johngarchie/xmas-icetube/firmware/config.h

#ifndef CONFIG_H
#define CONFIG_H

// XMAS-ICETUBE CLOCK DESIGN
//
// The xmas-icetube revision of the Ice Tube Clock requires a few
// firmware modifications.  The XMAS_DESIGN macro below enables these
// modifications, but breaks compatibility with the Adafruit Ice Tube
// Clock v1.1.
//
// When configuring this firmware for use with the xmas-icetube
// revision, the configuration macros for the following features
// should also be enabled:  the automatic dimmer hack, the software
// temperature compensated timekeeping, and the IV-18 to-spec hack.
//
//
// #define XMAS_DESIGN


// ADAFRUIT-STYLE BUTTONS
//
// By default, the xmas-icetube firmware uses a unique button scheme
// where there is one button mapped to each basic function:
//
//   enter/exit menu:  menu button
//   next:             plus button
//   select/set:       set button
//
// With the Adafruit button scheme, the buttons used for the first two
// functions depend on context:
//
//   enter/exit menu:  menu button when time is displayed,
//                     plus button when a menu label is displayed,
//                     menu button when a setting value is displayed
//   next:             menu button when a menu label is displayed,
//                     plus button when a setting value is displayed
//   select/set:       set button
//
// In addition to being simpler, the xmas button scheme works more
// intuitively with the xmas nested configuration menus.  Even so, some
// users still prefer the Adafruit scheme, typically for reasons of
// familiarity.  The following macro enables the Adafruit button scheme.
//
//
// #define ADAFRUIT_BUTTONS


// LOW BATTERY THRESHOLD
//
// After sleeping for ten minutes, system voltage should fall to whatever
// the battery is providing.  After that time, the microcontroller will
// check the system voltage.  If system voltage is below the following
// threshold, the clock will display a low battery warning ("bad batt")
// upon waking.
//
//
#define LOW_BATTERY_VOLTAGE 2600  // millivolts


// AUTOMATIC DIMMER HACK
//
// Defining the following macro enables support for Automatic dimming.
// This hack also allows for the clock display to be disabled at night
// (when dark).
//
// In the Adafruit Ice Tube Clock v1.1, this feature requires a
// pull-up resister to be installed in R4 and a CdS photoresistor to
// be installed in CT1.  CT1 is the two expansion pins nestled among
// L1, R4, and SPK.  I suggest using a 5.6k pull-up resistor with an
// Advanced Photonix Inc PDV-P8001 photoresistor.  Note that
// photoresistors purchased from Adafruit should behave like the
// PDV-P8001 and are acceptable substitutes.
//
// The automatic dimmer hack is discussed extensively on the
// Adafruit Clocks forum:
//
//   http://forums.adafruit.com/viewtopic.php?f=41&t=12932
//   http://forums.adafruit.com/viewtopic.php?p=219736#p219736
//
#define AUTOMATIC_DIMMER


// GPS TIMEKEEPING
//
// Defining the GPS_TIMEKEEPING macro below enables GPS detection on
// the ATmega's RX pin.  The connection speed is 9600 baud by default
// for compatibility with the Adafruit Ultimate GPS Module.  For more
// information, visit the following pages:
//
//   http://forums.adafruit.com/viewtopic.php?f=41&t=36873
//   http://www.ladyada.net/make/icetube/mods.html
//   http://forums.adafruit.com/viewtopic.php?f=41&t=32660
//
// In most cases, the clock should report an error if the GPS loses
// its fix.  But users with no GPS reception might want to disable the
// "gps lost" error message.  Those users will instead move their
// clocks to an area of good reception whenever they wish to
// syncronize the clock time with the GPS time.  To disable the GPS
// lost error message, comment out the GPS_LOST_ERROR_MSG macro below.
//
//
#define GPS_TIMEKEEPING
#define GPS_LOST_ERROR_MSG


// USART BAUD RATE
//
// The USART baud rate defined below is used for both the debugging
// output and GPS timekeeping.
//
//
#define USART_BAUDRATE 9600


// TEMPERATURE COMPENSATED CRYSTAL OSCILLATOR
//
// The following macro enables support for an external 32.768 kHz
// clock source such as a Maxim DS32kHz.  This hack is discussed in
// detail on the Adafruit Clocks forum:
//
//   http://forums.adafruit.com/viewtopic.php?f=41&t=14941
//
//
// #define EXTERNAL_CLOCK


// SOFTWARE TEMPERATURE COMPENSATED TIMEKEEPING
//
// This hack requires attaching a DS18B20 OneWire temperature sensor
// to ATmega328p PC1 pin, but unfortunately the internal temperature
// of the clock is above the ambient temperature.  As a result, this
// modification is not useful for displaying room temperature.
//
// This modification is, however, useful for temperature compensated
// timekeeping, and was primarily intended for the xmas-icetube
// hardware revision.  The DS32kHz, described in the previous section,
// is a simpler solution for the Adafruit Ice Tube Clock v1.1, but the
// DS18B20 will also work in the Adafruit design.   The DS18B20 should be
// installed in parasitic mode by grounding both the VDD and GND leads.
// The DQ lead should be connected to the PC1 pin on the ATmega328p and
// to PC5 via a 4.7k pull-up resistor.
//
// The XTAL_TURNOVER_TEMP macro specifies the temperature at which the
// crystal oscillates at maximum frequency in units of deg C / 16.
// The XTAL_FREQUENCY_COEF macro specifies the parabolic temperature
// dependence of the crystal in units -ppb / (deg C)^2.  For a
// turnover temperature of 25 deg C and a frequency coefficient of
// -0.034 ppm / (deg C)^2, XTAL_TURNOVER_TEMP should be defined as 400
// (25 * 16), and XTAL_FREQUENCY_COEF should be defined as 34
// (-0.034 * -1000).
//
// The technique for software temperature compensation is described in
// the following thread:
//
//   http://forums.adafruit.com/viewtopic.php?f=41&t=43998
//
// WARNING:  If your clock is modified for the original extended
// battery hack, which shorts the ATmega328P PC1 pin to ground,
// enabling the macros below might damage your clock!  The original
// extended battery hack is described in the following thread:
//
//   http://forums.adafruit.com/viewtopic.php?t=36697
// 
//
// #define TEMPERATURE_SENSOR
// #define XTAL_TURNOVER_TEMP  400  // deg C / 16
// #define XTAL_FREQUENCY_COEF 34   // -ppb / (deg C)^2


// BIRTHDAY ALARM
//
// If BDAY_ALARM_MONTH and BDAY_ALARM_DAY are defined, the alarm
// sound on that day will always be "For He's a Jolly Good Fellow,"
// regardless of the alarm sound set in the menus.
//
//
// #define BDAY_ALARM_MONTH 5
// #define BDAY_ALARM_DAY   1


// DISPLAY BRIGHTNESS / BOOST CONFIGURATION
//
// VFD displays lose brightness as they age, but increasing the
// grid/segment voltage can extend the useful life.  This voltage
// is controlled by the OCR0A register, and OCR0A is set by
//
//   OCR0A = OCR0A_MIN + OCR0A_SCALE * brightness
//
// where brightness is 0-10 as set through the configuration menu.
// The grid/segment voltage can be roughly estimated by
//
//   voltage = OCR0A / 4 + 6
//
// The IV-18 display has an absolute maximum grid/segment voltage of
// 70 volts, but on the Adafruit Ice Tube Clock, a Zener diode prevents
// this from exceeding 60 volts.  And the clock's fuse might blow before
// that point, so the hardware will ensure that the grid/segment voltage
// maximum is never exceeded.
//
// For a dim display, I suggest setting OCR0A_MIN to 30 and OCR0A_SCALE
// to 14.  If the fuse blows or becomes warm during operation, reduce
// OCR0A_SCALE or install a higher power fuse.
//
//
#define OCR0A_MIN   20
#define OCR0A_SCALE 11
#define OCR0A_MAX OCR0A_MIN + 10 * OCR0A_SCALE


// DISPLAY MULTIPLEXING ALGORITHM
//
// The following multiplexing options define how the display should be
// multiplexed.
//
// Digit multiplexing displays each digit in rapid succession.
// Although this is the standard way to do multiplexing, there might
// be slight ghosting, especially of decimals at higher boost voltage.
//
// I recommend digit multiplexing for use with the Adafruit Ice Tube
// Clock v1.1, without the to-spec hack.
//
// Subdigit multiplexing is similar to digit multiplexing, but
// displays each digit twice--once showing only segments B, C, and H
// (those lit when displaying "1.") and once showing only the other
// segments.  This method eliminates ghosting, but reduces overall
// brightness.
//
// I recommend subdigit multiplexing for use with the to-spec hack and
// the xmas-icetube hardware revision.  The reduction in overall
// brightness is a benefit here, as the minimum brightness attainable
// with PWM brightness control and digit multiplexing is a bit too
// bright.  And the maximum brightness with plain PWM and digit
// multiplexing is unnecessarally bright.
//
// Segment multiplexing displays each segment (on all digits where
// that segment is displayed) in rapid succession.  This method
// eliminates ghosting, and the maximum brightness is similar to that
// with digit multiplexing.  But the per-digit brightness adjustment
// is not available when using this method.
//
// I do not recommend segment multiplexing, but left the feature in
// the code in case anyone wants to play with it.  The problem with
// segment multiplexing is that resistance through the MAX6921
// limits current on each segment, so if one segment is displayed on
// many digits, that segment will be dimmer than if one segment is
// displayed on only a few digits.  Also, more current will flow
// through segments with the least resistance (at the right of the
// display), so those digits appear slightly brighter.
//
#define DIGIT_MULTIPLEXING
// #define SUBDIGIT_MULTIPLEXING
// #define SEGMENT_MULTIPLEXING


// IV-18 TO-SPEC HACK
//
// The Adafruit Ice Tube Clock v1.1 does not drive the IV-18 VFD tube
// to specifications, but with some rewiring and additional circuitry,
// enabling the following macros will drive the IV-18 tube as
// intended.  The following thread on the Adafruit Clocks forum
// describes the required hardware modifications for this hack:
//
//   http://forums.adafruit.com/viewtopic.php?f=41&t=41811
//
//
// #define VFD_TO_SPEC


// TO-SPEC BRIGHTNESS ADJUSTMENT METHOD
//
// These options should only be used with the to-spec hack above.
//
// With the to-spec hack, brightness may be controlled with boost
// voltage, pulse width modulation (PWM), or both.  I recommend
// controlling brightness with PWM only.
//
// If neither OCR0A_VALUE nor OCR0B_PWM_DISABLE is defined, brightness
// will be controlled by both boost voltage and PWM.
//
// If only OCR0A_VALUE is defined, the boost voltage will be fixed,
// and brightness will be controlled by PWM (recommended).
//
// If only OCR0B_PWM_DISABLE is defined, brightness will be controlled
// by the boost voltage.
//
// Defining OCR0A_VALUE and OCR0B_PWM_DISABLE is possible, but doing
// so will lock the display to a constant brightness and break the
// menu-configurable brightness adjustment.
//
// If D1 is a power blocking diode (as in the xmas-icetube hardware
// revision), I suggest an OCR0A_VALUE of 192.  If D1 is a Schottky
// diode (as in the original Adafruit design), I suggest an OCR0A_VALUE
// value of 128.  Ideally, the exact value should be tuned for your
// particular clock:  OCR0A_VALUE should be large enough such that the
// boost circuit generates just over 50v with the display installed
// and at maximum brightness, but OCR0A_VALUE should be no larger than
// necessary to prevent excessive voltage from being lost through the
// Zener diode.
//
//
// #define OCR0A_VALUE 128
// #define OCR0B_PWM_DISABLE


// TO-SPEC FILAMENT DRIVER METHOD
//
// The options below should only be used with the to-spec hack above.
// To drive the filament to specifications, do not define any of the
// filament current or voltage macros below.
//
// Some tubes may make a humming or whining sound when driven with AC.
// If the noise is unacceptable, the frequency can be divided with
// FILAMENT_FREQUENCY_DIV.  For example, if FILAMENT_FREQUENCY_DIV macro
// is defined as 3, the AC frequency will be 12/3 = 4 kHz.  The AC
// frequency may be divided by any value below 256.
//
// Although not to-spec, a sure-fire way to eliminate hum is to simply
// drive the filament with DC.  With a high boost voltage, there
// should not be a noticeable brightness gradient.
//
// Defining the FILAMENT_DRIVE_DC_FWD macro will drive the display
// with direct current instead of alternating current.  Current will
// flow from right to left across the display.  Defining the
// FILAMENT_DRIVE_DC_REV macro will use direct current flowing from
// left to right across the display.
//
// Defining either FILAMENT_VOLTAGE_3_3 or FILAMENT_VOLTAGE_2_5 will
// reduce the filament voltage to either 3.3 or 2.5 volts,
// respectively.  Voltage is reduced by changing the duty cycle from
// 100% to either 66% or 50%.  These macros also affect drive
// frequency; if the FILAMENT_FREQUENCY_DIV macro is undefined (or
// defined as 1), the frequency will be approximately
//
//              ALTERNATING CURRENT    DIRECT CURRENT
// 5.0 VOLTS          13.0 kHz              --
// 3.3 VOLTS           9.0 kHz             9.0 kHz
// 2.5 VOLTS           6.5 kHz            13.0 kHz
//
// And again, defining any of the voltage or current macros below
// deliberately runs the filament outside the IV-18 specifications.
// These macros are mainly provided for testing purposes.  But if the
// reddish glow of the filament is bothersome, reducing the filament
// voltage might be worthwhile even though doing so may cause cathode
// poisoning.  Another option to reduce the reddish glow is to have
// the case made from blue tinted acrylic.
//
//
// #define FILAMENT_FREQUENCY_DIV 3
//
// #define FILAMENT_CURRENT_DC_FWD
// #define FILAMENT_CURRENT_DC_REV
//
// #define FILAMENT_VOLTAGE_3_3
// #define FILAMENT_VOLTAGE_2_5


// AUTOMATIC DRIFT CORRECTION
//
// As the user changes time to correct for time error, the clock will
// eventually determine how fast or slow the crystal oscillates and
// use this information to correct for time drift.  A more detailed
// description of the automatic drift correction algorithm is given
// in the following post:
//
//   http://forums.adafruit.com/viewtopic.php?p=178611#p178611
//
// If one already knows how fast or slow the clock runs without drift
// correction, one can preload this information so that the clock will
// keep accurate time immediately after flashing.
//
// The desired drift correction is defined by a single number.  The
// magnitude (absolute value) defines how often a 1/128 second
// correction must be made in seconds.  If the clock is slow, time
// must be adjusted *forward*, so the sign should be *positive*.  If
// the clock is fast, time must be adjusted *backward*, so the sign
// should be *negative*.  A drift correction value of zero indicates
// that no drift correction should be performed.
//
// For example, assume a clock runs slow by 3 seconds per day, typical
// of an unmodified Adafruit Ice Tube Clock.  To compensate, the clock
// must make 3 * 128 = 384 corrections per day, since each correction
// is 1/128 seconds.  Those corrections must be made over one day or
// 24 * 60 * 60 = 86400 seconds.  Therefore, the clock should make
// corrections at intervals of 86400 / 384 = 255 seconds.  Because the
// clock runs slow, the drift correction value should be positive 255.
//
// Defining a drift correction value with AUTODRIFT_PRELOAD enables
// drift correction by the specified amount immediately after
// programming.  But the clock will still determine if it is running
// fast or slow with the user changes the time.  This behavior will
// allow the clock to automatically refine the preloaded drift
// correction value and adapt to changes crystal frequency over time.
//
// Defining a drift correction value with AUTODRIFT_CONSTANT also
// enables drift correction immediately after programming, but the
// clock will always use the specified drift correction value.  The
// clock will not automatically determine if it is running fast or
// slow when the user changes the time.
//
// Defining the AUTODRIFT_CONSTANT macro as zero will completely
// disable drift correction.
//
//
// #define AUTODRIFT_PRELOAD  255
// #define AUTODRIFT_CONSTANT 0


// SLEEP DRIFT CORRECTION VALUE
//
// At lower voltages, oscillator circuits tend to operate at lower
// frequencies, so the oscillator will run slightly slower during
// sleep.  The AUTODRIFT_SLEEP provides an additional drift correction
// value to be applied during sleep.  Note that this correction is
// applied *in addition* to the normal drift correction method.
//
//
#ifdef EXTERNAL_CLOCK
#define AUTODRIFT_SLEEP 1600  // ~5 ppm
#else
#define AUTODRIFT_SLEEP 2800  // ~2.8 ppm
#endif


// DEBUGGING FEATURES
//
// The following macro enables debugging.  When enabled, debugging
// information may be transmitted over USART via the DUMPINT() and
// DUMPSTR() macros defined in usart.h.  The baud rate is specified by
// the USART_BAUDRATE macro, which is defined earlier in this file.
//
//
// #define DEBUG


#endif  // CONFIG_H
