johngarchie/xmas-icetube/firmware/display.h

#ifndef DISPLAY_H
#define DISPLAY_H

#include <stdint.h>        // for using standard integer types
#include <avr/pgmspace.h>  // for accessing data in program memory

#include "config.h"  // for configuration macros
#include "temp.h"    // to compensate for timing errors
		     // while determining temperature


#define DISPLAY_SIZE 9
#define SEGMENT_COUNT 8
#define DISPLAY_OFF_TIMEOUT 60

// status flags for display.status
#define DISPLAY_ANIMATED	0x01  // animated display transitions
#define DISPLAY_ZEROPAD		0x02  // zero-pad all numbers
#define DISPLAY_ALTNINE		0x04  // alternative display for 9s
#define DISPLAY_ALTALPHA	0x08  // alternative capital alphabet
#define DISPLAY_PULSING		0x10  // display brightness pulsing
#define DISPLAY_PULSE_DOWN	0x20  // display brightness dimming
#define DISPLAY_DISABLED	0x40  // display disabled
#define DISPLAY_HIDEDOTS	0x80  // hide flashing dot separators

// savable settings in lower nibble of display.status
#define DISPLAY_SETTINGS_MASK 0x0F

#ifdef VFD_TO_SPEC
// time required for one step of OCR0B when pulsing
#define DISPLAY_PULSE_DELAY 750 / 81  // (semiticks)
#else  // ~VFD_TO_SPEC
// time required for one step of OCR0A when pulsing
#define DISPLAY_PULSE_DELAY 750 / (OCR0A_MAX - OCR0A_MIN)  // (semiticks)
#endif  // VFD_TO_SPEC

#ifdef SUBSEGMENT_MULTIPLEXING
#define DISPLAY_NOFLICKER_TIME 128
#else  // ~SUBSEGMENT_MULTIPLEXING
#define DISPLAY_NOFLICKER_TIME 256
#endif  // SUBSEGMENT_MULTIPLEXING

// time between photoresister voltage samples
#define DISPLAY_ADC_DELAY 16  // (semiticks)

// disabled flag for display.off_hour
#define DISPLAY_NOOFF 0x80

// the largest value for a rolling colon
#define DISPLAY_ROLLING_MAX 2


// types of display transitions
enum {
    DISPLAY_TRANS_NONE,
    DISPLAY_TRANS_INSTANT,
    DISPLAY_TRANS_UP,
    DISPLAY_TRANS_DOWN,
    DISPLAY_TRANS_LEFT,
};

// duration of each left/right or up/down transiton step
#define DISPLAY_TRANS_LR_DELAY 20  // (semiticks)
#define DISPLAY_TRANS_UD_DELAY 50  // (semiticks)

// duration of blinking dot times
#define DISPLAY_DOTFLASH_SLOW_TIME  768  // (semiticks)
#define DISPLAY_DOTFLASH_FAST_TIME  384  // (semiticks)


typedef struct {
    uint8_t status;                 // display status flags

    uint8_t multiplex_div;	    // the multiplexing timer
    uint8_t trans_type;             // current transition type
    uint8_t trans_timer;            // current transition timer
    uint8_t prebuf[DISPLAY_SIZE];   // future display contents
    uint8_t postbuf[DISPLAY_SIZE];  // current display contents

    int16_t  colon_timer;	    // transition timer for colon animations
    uint8_t  colon_prebuf;	    // bitmask for future colon indexes
    uint8_t  colon_postbuf;	    // bitmask for future colon indexes
    uint8_t  colon_style_idx;	    // the selected colon style index
    uint16_t colon_frame;	    // current colon frame data
    uint8_t  colon_frame_idx;	    // current colon frame index

    int16_t  dot_timer;		    // transition timer for blinking dots
    uint8_t  dot_prebuf;	    // bitmask for future dot indexes
    uint8_t  dot_postbuf;	    // bitmask for current dot indexes

#ifdef AUTOMATIC_DIMMER
    int8_t  bright_min;             // minimum display brightness
    int8_t  bright_max;             // maximum display brightness

    // display turns off during wake mode when photosensor is below
    // 256 * threshold and the display-off timer is expired
    uint8_t off_threshold;         // display-off threshold

    // photoresistor adc result (times 2^6, running average)
    uint16_t photo_avg;

    // current brightness level from photoresistor
    // (truncated to [0, 80] for actual display brightness)
    int16_t photo_idx;
#else
    int8_t  brightness;             // display brightness
#endif  // AUTOMATIC_DIMMER

    // off time:  disable display after off_hour and off_minute;
    //            enable display after on_hour and on_minute
    // off time is disabled when the highest bit, DISPLAY_NOOFF, is set
    uint8_t off_hour;  uint8_t off_minute;
    uint8_t on_hour;   uint8_t on_minute;

    // off_days and on_days are bits specifying when the display should
    // be explicitly enabled or disabled, overriding the usual off time
    // preferences.  For example, weekends would be specified by
    //    _BV(TIME_SUN) | _BV(TIME_SAT)
    uint8_t off_days;  // disable display on given days
    uint8_t on_days;   // ignore off time on given days

    // when display is disabled, any button press enables the display
    // for DISPLAY_OFF_TIMEOUT seconds.  off_timer stores the number
    // of seconds before the display may be disabled after a button press.
    uint8_t off_timer;

#ifdef VFD_TO_SPEC
    uint8_t filament_timer;   // timer for generating filament current
    uint8_t filament_div;     // divider counter for filament frequency
    uint8_t filament_div_max; // max value for divider counter

#ifndef OCR0B_PWM_DISABLE
    uint8_t OCR0B_value;
#endif  // ~OCR0B_PWM_DISABLE
#endif  // VFD_TO_SPEC

#ifndef SEGMENT_MULTIPLEXING
    // length of time to display each digit (32 microsecond units)
    uint8_t digit_times[DISPLAY_SIZE];
    uint8_t digit_time_shift;  // flicker reduction adjustment
#endif  // ~SEGMENT_MULTIPLEXING
} display_t;

volatile extern display_t display;


void display_init(void);
void display_wake(void);
void display_sleep(void);

void display_tick(void);

void display_off(void);
void display_on(void);

uint8_t display_varsemitick(void);
void display_semitick(void);

// toggle push-pull outputs to generate alternating current on vfd fillament
static inline void display_semisemitick(void) {
    // multiplex the display
    if(display.multiplex_div && !--display.multiplex_div) {
	display.multiplex_div = display_varsemitick();
    }
#ifdef TEMPERATURE_SENSOR
    while(temp.missed_ovf) {
	--temp.missed_ovf;
	if(display.multiplex_div && !--display.multiplex_div) {
	    display.multiplex_div = display_varsemitick();
	}
    }
#endif  // TEMPERATURE_SENSOR

    // generate ac-filament current as required
#if defined(VFD_TO_SPEC)
    if(!(display.status & DISPLAY_DISABLED)) {
	if( display.filament_div && !--display.filament_div ) {
#if defined(FILAMENT_CURRENT_DC_FWD)
#if defined(FILAMENT_VOLTAGE_3_3)
	    switch(display.filament_timer) {
		case 0:
		    PORTC &= ~_BV(PC2);
		    PORTC |=  _BV(PC3);
		case 1:
		    ++display.filament_timer;
		    break;
		default:
		    PORTC &= ~_BV(PC2);
		    PORTC &= ~_BV(PC3);
		    display.filament_timer = 0;
		    break;
	    }
#elif defined(FILAMENT_VOLTAGE_2_5) // && !defined(FILAMENT_VOLTAGE_3_3)
	    switch(display.filament_timer) {
		case 0:
		    PORTC &= ~_BV(PC2);
		    PORTC |=  _BV(PC3);
		    ++display.filament_timer;
		    break;
		default:
		    PORTC &= ~_BV(PC2);
		    PORTC &= ~_BV(PC3);
		    display.filament_timer = 0;
		    break;
	    }
#else  // ~FILAMENT_VOLTAGE_3_3 && ~FILAMENT_VOLTAGE_2_5 
	    PORTC &= ~_BV(PC2);
	    PORTC |=  _BV(PC3);
#endif  // FILAMENT_VOLTAGE_*

#elif defined(FILAMENT_CURRENT_DC_REV) // && !defined(FILAMENT_CURRENT_DC_FWD)

#if defined(FILAMENT_VOLTAGE_3_3)
	    switch(display.filament_timer) {
		case 0:
		    PORTC |=  _BV(PC2);
		    PORTC &= ~_BV(PC3);
		case 1:
		    ++display.filament_timer;
		    break;
		default:
		    PORTC &= ~_BV(PC2);
		    PORTC &= ~_BV(PC3);
		    display.filament_timer = 0;
		    break;
	    }
#elif defined(FILAMENT_VOLTAGE_2_5) // && !defined(FILAMENT_VOLTAGE_3_3)
	    switch(display.filament_timer) {
		case 0:
		    PORTC |=  _BV(PC2);
		    PORTC &= ~_BV(PC3);
		    ++display.filament_timer;
		    break;
		default:
		    PORTC &= ~_BV(PC2);
		    PORTC &= ~_BV(PC3);
		    display.filament_timer = 0;
		    break;
	    }
#else  // ~FILAMENT_VOLTAGE_3_3 && ~FILAMENT_VOLTAGE_2_5 
	    PORTC |=  _BV(PC2);
	    PORTC &= ~_BV(PC3);
#endif  // FILAMENT_VOLTAGE_*

#else  // ~FLIAMENT_CURRENT_DC_REV && ~FILAMENT_CURRENT_DC_FWD

#ifdef FILAMENT_VOLTAGE_3_3
	    switch(display.filament_timer) {
		case 0:
		    PORTC &= ~_BV(PC2);
		    PORTC |=  _BV(PC3);
		    ++display.filament_timer;
		    break;
		case 1:
		    PORTC |=  _BV(PC2);
		    PORTC &= ~_BV(PC3);
		    ++display.filament_timer;
		    break;
		default:
		    PORTC &= ~_BV(PC2);
		    PORTC &= ~_BV(PC3);
		    display.filament_timer = 0;
		    break;
	    }
#elif defined(FILAMENT_VOLTAGE_2_5) // && !defined(FILAMENT_VOLTAGE_3_3)
	    switch(display.filament_timer) {
		case 0:
		    PORTC |=  _BV(PC2);
		    PORTC &= ~_BV(PC3);
		    ++display.filament_timer;
		    break;
		case 1:
		    PORTC &= ~_BV(PC2);
		    PORTC &= ~_BV(PC3);
		    ++display.filament_timer;
		    break;
		case 2:
		    PORTC &= ~_BV(PC2);
		    PORTC |=  _BV(PC3);
		    ++display.filament_timer;
		    break;
		default:
		    PORTC &= ~_BV(PC2);
		    PORTC &= ~_BV(PC3);
		    display.filament_timer = 0;
		    break;
	    }
#else // ~FILAMENT_VOLTAGE_3_3 && ~FILAMENT_VOLTAGE_2_5
	    switch(display.filament_timer) {
		case 0:
		    PORTC |=  _BV(PC2);
		    PORTC &= ~_BV(PC3);
		    ++display.filament_timer;
		    break;
		default:
		    PORTC &= ~_BV(PC2);
		    PORTC |=  _BV(PC3);
		    display.filament_timer = 0;
		    break;
	    }
#endif  // FILAMENT_VOLTAGE_3_3
#endif // FILAMENT_CURRENT_DC_*

#ifdef FILAMENT_FREQUENCY_DIV
	    display.filament_div = FILAMENT_FREQUENCY_DIV;
#else  // ~FILAMENT_FREQUENCY_DIV
	    display.filament_div = 1;
#endif // FILAMENT_FREQUENCY_DIV
	}
    }
#endif  // VFD_TO_SPEC
}

void display_savestatus(void);
void display_loadstatus(void);

void display_savecolonstyle(void);
void display_loadcolonstyle(void);
void display_nextcolonstyle(void);
void display_loadcolonframe(void);
void display_nextcolonframe(void);
void display_updatecolons(void);

void display_nextdotstyle(void);
void display_updatedots(void);

void display_loadbright(void);
void display_savebright(void);

void display_loaddigittimes(void);
void display_savedigittimes(void);

void display_noflicker(void);

#ifdef AUTOMATIC_DIMMER
void display_loadphotooff(void);
void display_savephotooff(void);
#endif  // AUTOMATIC_DIMMER

void display_loadofftime(void);
void display_saveofftime(void);

void display_loadoffdays(void);
void display_saveoffdays(void);

void display_loadondays(void);
void display_saveondays(void);

uint8_t display_onbutton(void);

void display_autodim(void);
void display_setbrightness(int8_t level);

void display_pstr(const uint8_t idx, PGM_P pstr);
void display_digit(uint8_t idx, uint8_t n);
void display_twodigit_rightadj(uint8_t idx, int8_t n);
void display_twodigit_leftadj(uint8_t idx, int8_t n);
void display_twodigit_zeropad(uint8_t idx, int8_t n);
void display_char(uint8_t idx, char c);
void display_clear(uint8_t idx);

void display_clearall(void);
void display_dotselect(uint8_t idx_start, uint8_t idx_end);
void display_dot(uint8_t idx, uint8_t show);
void display_dotsep(uint8_t idx, uint8_t show);
void display_dash(uint8_t idx, uint8_t show);
void display_dial(uint8_t idx, uint8_t seconds);

void display_transition(uint8_t type);

#endif
